sergejbubko/HODLcube/CoinbaseApi.h

/*
Copyright (c) 2017 Brian Lough. All right reserved.

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
You should have received a copy of the GNU Lesser General Public
License along with this library; if not, write to the Free Software
Foundation, Inc., 51 Franklin St, Fifth Floor, Boston, MA 02110-1301 USA
*/


#ifndef CoinbaseApi_h
#define CoinbaseApi_h

#include <Arduino.h>
#include <ArduinoJson.h>
#include <WiFiClientSecure.h>

#define COINBASE_HOST "api.exchange.coinbase.com"

struct CBPTickerResponse{
  float price;
  String error;
};

struct CBPStatsResponse{
  float open;
  float high;
  float low;
  String error;
};

struct CBPCandlesResponse{
  float open;
  String error;
};


class CoinbaseApi
{
  public:
    CoinbaseApi (WiFiClientSecure &client);
    String SendGetToCoinbase(String &command);
    CBPTickerResponse GetTickerInfo(String &coinId);
    CBPStatsResponse GetStatsInfo(String &coinId);
    CBPCandlesResponse GetCandlesInfo(String &tickerId, String &date);
    int Port = 443;

  private:
    CBPTickerResponse responseTickerObject;
    CBPStatsResponse responseStatsObject;
    CBPCandlesResponse responseCandlesObject;
    WiFiClientSecure *client;
    void closeClient();
};

#endif
